Squalius-cephalus/silakka44/firmware/silakka44/keymaps/vial/config.h

/* SPDX-License-Identifier: GPL-2.0-or-later */

#pragma once

#define VIAL_KEYBOARD_UID {0x5C, 0x70, 0x53, 0x55, 0xB8, 0x9F, 0xEF, 0x32}

#define VIAL_UNLOCK_COMBO_ROWS { 0, 1 }
#define VIAL_UNLOCK_COMBO_COLS { 1, 1 }
